rvkshn-10/Keyboard/keyboard61/inward-usb/screenshots/04-checks.jpg

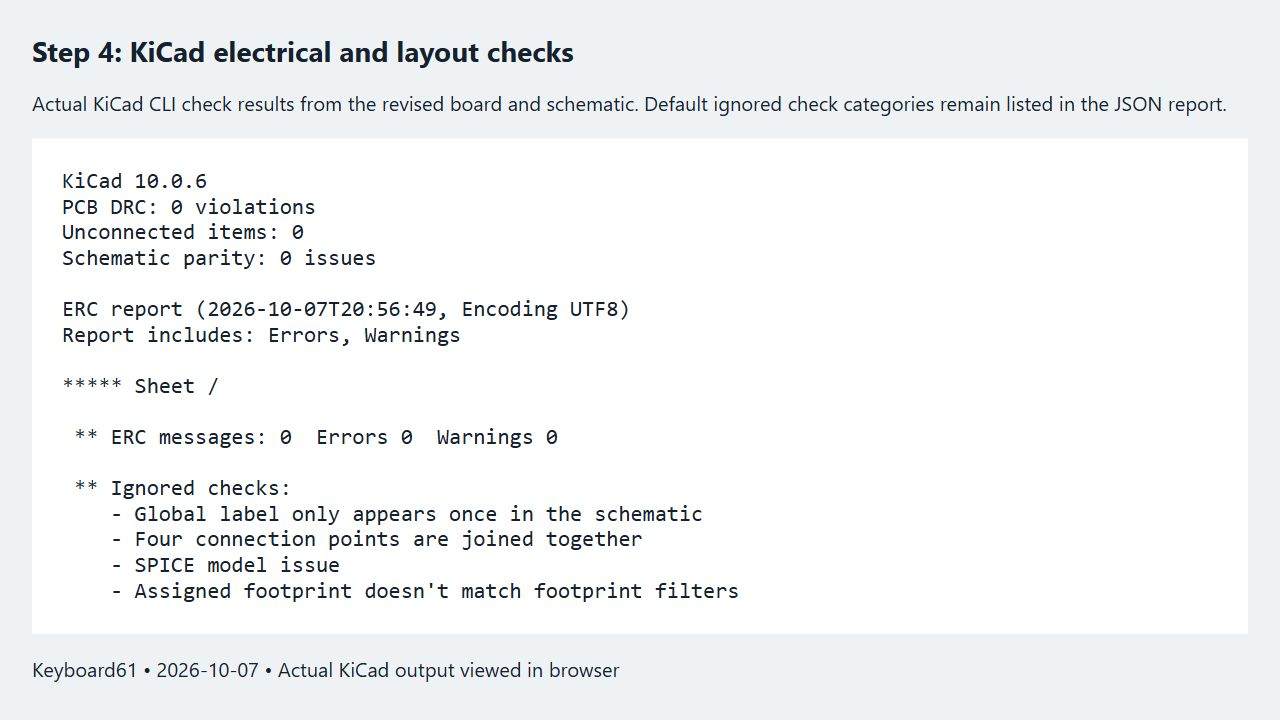
keyboard61/inward-usb/screenshots/04-checks.jpg
